peterb154/f150-temperature/include/colors.h

#ifndef COLORS_H
#define COLORS_H

// Colors
#define COLOR_SUCCESS    0x07E0
#define COLOR_BACKGROUND 0x0841   // Dark blue-grey
#define COLOR_CARD_BG    0x2124   // Lighter grey for cards
#define COLOR_PRIMARY    0x07FF   // Cyan
#define COLOR_TEXT       0xFFFF   // White
#define COLOR_COLD       0x249F   // Light blue
#define COLOR_WARM       0xFD20   // Orange
#define COLOR_HOT        0xF800   // Red
#define COLOR_ACCENT     0x07E0   // Green
#define COLOR_WARNING    0xFFE0   // Yellow

#endif // COLORS_H
